zhong123456789/xds100v3-anlogic/HDL/hdl/pll_x48.vhd

-- Version: 9.0 9.0.0.15

library ieee;
use ieee.std_logic_1164.all;
library proasic3;
use proasic3.all;


entity pll_x48 is 

port(
POWERDOWN, CLKA : in std_logic;  
LOCK, GLA : out std_logic) ;
end pll_x48;


architecture DEF_ARCH of  pll_x48 is

component PLL

generic (VCOFREQUENCY:real := 0.0);

port(
CLKA, EXTFB, POWERDOWN : in std_logic := 'U'; 
GLA, LOCK, GLB, YB, GLC, YC : out std_logic; 
OADIV0, OADIV1, OADIV2, OADIV3, OADIV4, OAMUX0, OAMUX1, OAMUX2, DLYGLA0, 
DLYGLA1, DLYGLA2, DLYGLA3, DLYGLA4, OBDIV0, OBDIV1, 
OBDIV2, OBDIV3, OBDIV4, OBMUX0, OBMUX1, OBMUX2, DLYYB0, 
DLYYB1, DLYYB2, DLYYB3, DLYYB4, DLYGLB0, DLYGLB1, DLYGLB2, 
DLYGLB3, DLYGLB4, OCDIV0, OCDIV1, OCDIV2, OCDIV3, OCDIV4, 
OCMUX0, OCMUX1, OCMUX2, DLYYC0, DLYYC1, DLYYC2, DLYYC3, 
DLYYC4, DLYGLC0, DLYGLC1, DLYGLC2, DLYGLC3, DLYGLC4, 
FINDIV0, FINDIV1, FINDIV2, FINDIV3, FINDIV4, FINDIV5, 
FINDIV6, FBDIV0, FBDIV1, FBDIV2, FBDIV3, FBDIV4, FBDIV5, 
FBDIV6, FBDLY0, FBDLY1, FBDLY2, FBDLY3, FBDLY4, FBSEL0, 
FBSEL1, XDLYSEL, VCOSEL0, VCOSEL1, VCOSEL2 : in std_logic := 'U') ;

end component;



component VCC
port( Y : out std_logic);
end component;

component GND
port( Y : out std_logic);
end component;


signal VCC_1_net, GND_1_net : std_logic ;

begin   


VCC_2_net : VCC port map(Y => VCC_1_net);
GND_2_net : GND port map(Y => GND_1_net);

Core : PLL
generic map(VCOFREQUENCY => 100.656)
port map(
CLKA => CLKA, 
EXTFB => GND_1_net, 
POWERDOWN => POWERDOWN, 
GLA => GLA, 
LOCK => LOCK, 
GLB => OPEN , 
YB => OPEN , 
GLC => OPEN , 
YC => OPEN , 
OADIV0 => GND_1_net, 
OADIV1 => GND_1_net, 
OADIV2 => GND_1_net, 
OADIV3 => GND_1_net, 
OADIV4 => GND_1_net, 
OAMUX0 => GND_1_net, 
OAMUX1 => GND_1_net, 
OAMUX2 => VCC_1_net, 
DLYGLA0 => GND_1_net, 
DLYGLA1 => GND_1_net, 
DLYGLA2 => GND_1_net, 
DLYGLA3 => GND_1_net, 
DLYGLA4 => GND_1_net,
OBDIV0 => GND_1_net, 
OBDIV1 => GND_1_net, 
OBDIV2 => GND_1_net, 
OBDIV3 => GND_1_net, 
OBDIV4 => GND_1_net, 
OBMUX0 => GND_1_net, 
OBMUX1 => GND_1_net, 
OBMUX2 => GND_1_net, 
DLYYB0 => GND_1_net, 
DLYYB1 => GND_1_net, 
DLYYB2 => GND_1_net, 
DLYYB3 => GND_1_net, 
DLYYB4 => GND_1_net, 
DLYGLB0 => GND_1_net, 
DLYGLB1 => GND_1_net, 
DLYGLB2 => GND_1_net, 
DLYGLB3 => GND_1_net,
DLYGLB4 => GND_1_net, 
OCDIV0 => GND_1_net, 
OCDIV1 => GND_1_net, 
OCDIV2 => GND_1_net, 
OCDIV3 => GND_1_net, 
OCDIV4 => GND_1_net, 
OCMUX0 => GND_1_net, 
OCMUX1 => GND_1_net, 
OCMUX2 => GND_1_net, 
DLYYC0 => GND_1_net, 
DLYYC1 => GND_1_net, 
DLYYC2 => GND_1_net, 
DLYYC3 => GND_1_net, 
DLYYC4 => GND_1_net, 
DLYGLC0 => GND_1_net, 
DLYGLC1 => GND_1_net, 
DLYGLC2 => GND_1_net, 
DLYGLC3 => GND_1_net, 
DLYGLC4 => GND_1_net, 
FINDIV0 => GND_1_net, 
FINDIV1 => GND_1_net, 
FINDIV2 => GND_1_net, 
FINDIV3 => GND_1_net, 
FINDIV4 => GND_1_net, 
FINDIV5 => GND_1_net, 
FINDIV6 => GND_1_net, 
FBDIV0 => VCC_1_net, 
FBDIV1 => VCC_1_net, 
FBDIV2 => VCC_1_net, 
FBDIV3 => VCC_1_net, 
FBDIV4 => GND_1_net, 
FBDIV5 => VCC_1_net, 
FBDIV6 => GND_1_net, 
FBDLY0 => GND_1_net, 
FBDLY1 => VCC_1_net, 
FBDLY2 => VCC_1_net, 
FBDLY3 => GND_1_net, 
FBDLY4 => GND_1_net,
FBSEL0 => GND_1_net, 
FBSEL1 => VCC_1_net, 
XDLYSEL => GND_1_net, 
VCOSEL0 => GND_1_net, 
VCOSEL1 => GND_1_net, 
VCOSEL2 => VCC_1_net);

end DEF_ARCH;
